Rootthecause/HVI/doc/Pictures and Renderings/HVI 3 Top angle.png

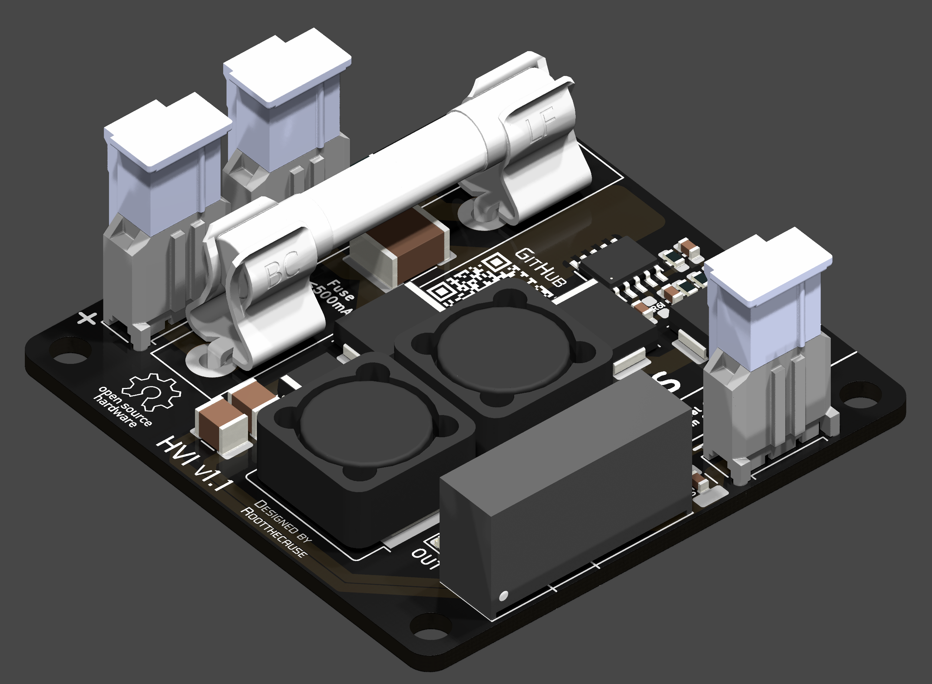
doc/Pictures and Renderings/HVI 3 Top angle.png
