Rootthecause/HVI/doc/Pictures and Renderings/HVI 4 Bottom angle.png

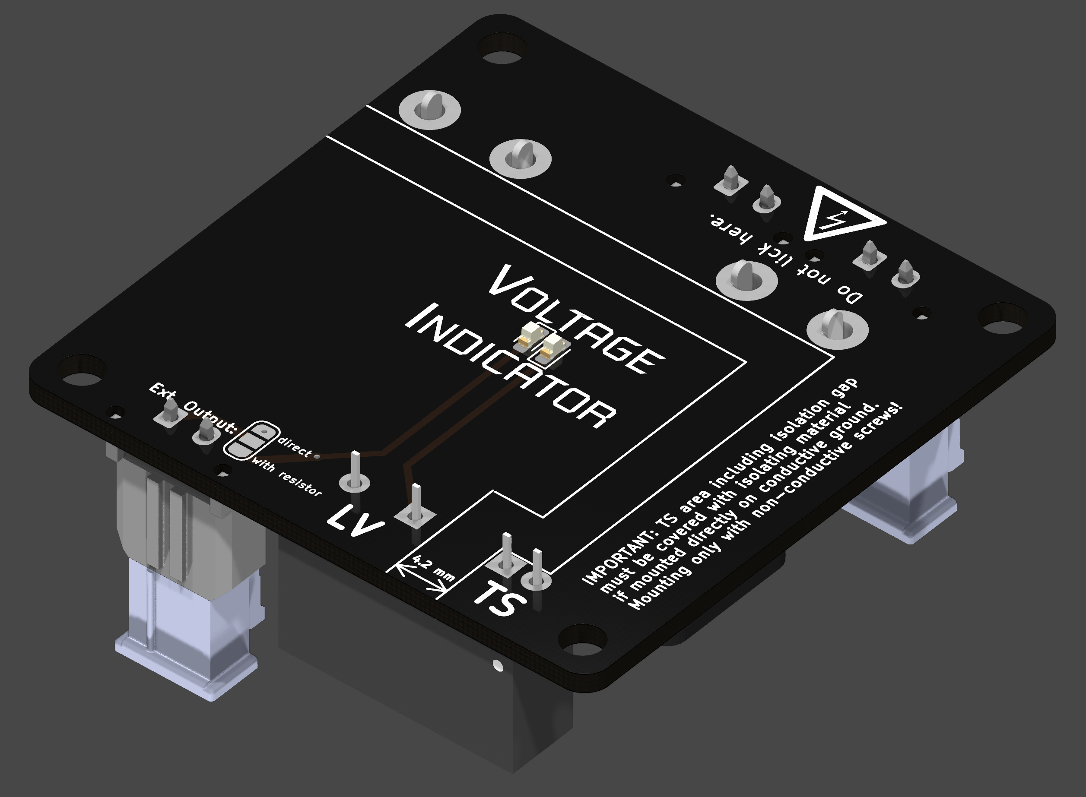
doc/Pictures and Renderings/HVI 4 Bottom angle.png
