Rootthecause/HVI/doc/Pictures and Renderings/HVI Top with case.jpg

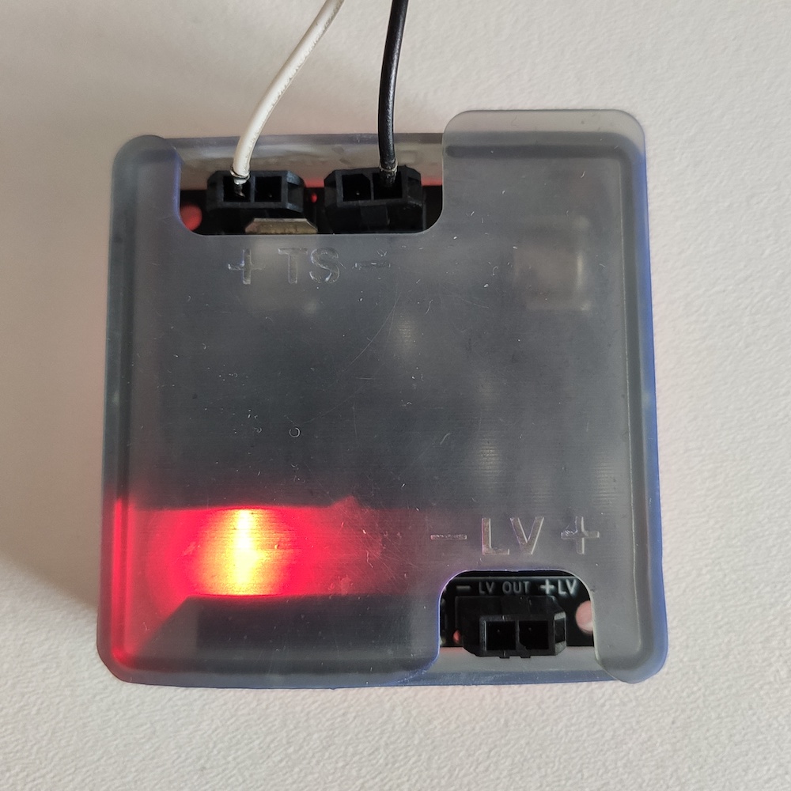
doc/Pictures and Renderings/HVI Top with case.jpg
