Rootthecause/HVI/doc/Gerber Files for JLC Order/JLC Order Settings 1.jpg

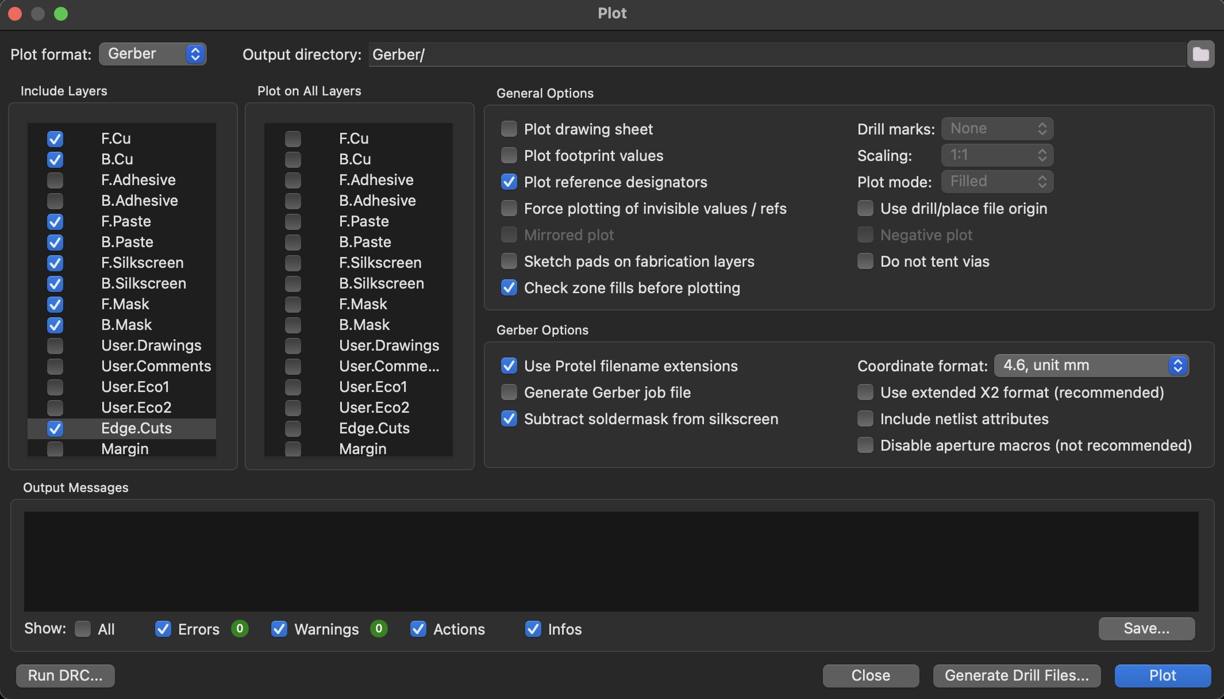
doc/Gerber Files for JLC Order/JLC Order Settings 1.jpg
