Rootthecause/HVI/doc/Gerber Files for JLC Order/JLC Order Settings 2.jpg

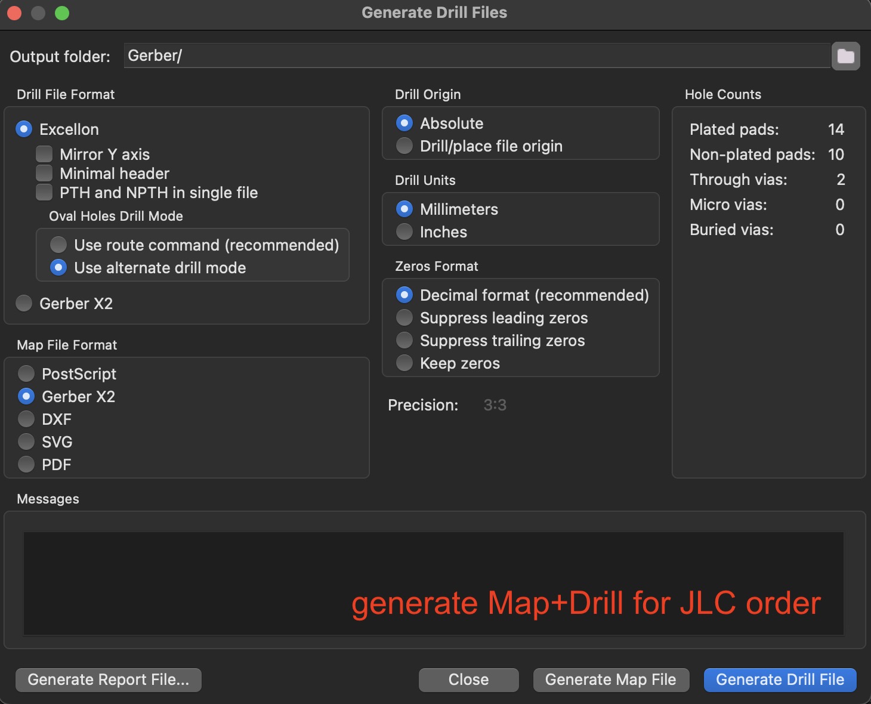
doc/Gerber Files for JLC Order/JLC Order Settings 2.jpg
